4dragunov/leaksensor/src/apps/LeakDetector/SRWLD02/sensors.h

/*
 * sensors.h
 *
 *  Created on: Feb 3, 2025
 *      Author: Andrey
 */

#ifndef SRC_APPS_SMARTROOF_LORA_NODE_LEAKDETECTOR_SRWLD01_SENSORS_H_
#define SRC_APPS_SMARTROOF_LORA_NODE_LEAKDETECTOR_SRWLD01_SENSORS_H_
#include <chrono>
#include "sensors-board.h"
#define MAX_DS18B20_SENSOR_COUNT 8
typedef struct {
	int16_t data[MAX_DS18B20_SENSOR_COUNT];
	uint8_t sensors;
	std::chrono::time_point<std::chrono::system_clock> timestamp;
} ThermalSensorsData ;

typedef struct{
	Samples leakSamples;
	ThermalSensorsData thermal;
	std::chrono::time_point<std::chrono::system_clock> timestamp;
}SummarySensorsData;

extern osMailQId  gSummarySensorsMq;

struct SummarySensorsDataMailDeleter {
    void operator()(SummarySensorsData* p) const {
        //std::cout << std::endl;
        osMailFree(gSummarySensorsMq, p);
    }
};
typedef std::shared_ptr<SummarySensorsData> SummarySensorsDataSharedMail;

#endif /* SRC_APPS_SMARTROOF_LORA_NODE_LEAKDETECTOR_SRWLD01_SENSORS_H_ */
