4dragunov/leaksensor/src/boards/SRWLD01/board-config.h

/*!
 * \file      board-config.h
 *
 * \brief     Board configuration
 *
 * \copyright Revised BSD License, see section \ref LICENSE.
 *
 * \code
 *                ______                              _
 *               / _____)             _              | |
 *              ( (____  _____ ____ _| |_ _____  ____| |__
 *               \____ \| ___ |    (_   _) ___ |/ ___)  _ \
 *               _____) ) ____| | | || |_| ____( (___| | | |
 *              (______/|_____)_|_|_| \__)_____)\____)_| |_|
 *              (C)2013-2017 Semtech
 *
 *               ___ _____ _   ___ _  _____ ___  ___  ___ ___
 *              / __|_   _/_\ / __| |/ / __/ _ \| _ \/ __| __|
 *              \__ \ | |/ _ \ (__| ' <| _| (_) |   / (__| _|
 *              |___/ |_/_/ \_\___|_|\_\_| \___/|_|_\\___|___|
 *              embedded.connectivity.solutions===============
 *
 * \endcode
 *
 * \author    Miguel Luis ( Semtech )
 *
 * \author    Gregory Cristian ( Semtech )
 *
 * \author    Daniel Jaeckle ( STACKFORCE )
 *
 * \author    Johannes Bruder ( STACKFORCE )
 */
#ifndef __BOARD_CONFIG_H__
#define __BOARD_CONFIG_H__

#include "gpio.h"
#include "adc.h"
#include "OneWire.h"
#include "ds18b20.h"
#include "modbus.h"
#include "eeprom.h"
#include "sensors-board.h"
/*!
 * Defines the time required for the TCXO to wakeup [ms].
 */
#if defined( SX1262MBXDAS )
#define BOARD_TCXO_WAKEUP_TIME                      5
#else
#define BOARD_TCXO_WAKEUP_TIME                      0
#endif

/*!
 * Board MCU pins definitions
 */
#define RADIO_RESET                                 PB_12

#define RADIO_MOSI                                  PB_15
#define RADIO_MISO                                  PB_14
#define RADIO_SCLK                                  PB_13

#if defined( SX1272MB2DAS) || defined( SX1276MB1LAS ) || defined( SX1276MB1MAS )

#define RADIO_NSS                                   PD_8

#define RADIO_DIO_0                                 PE_6
#define RADIO_DIO_1                                 PE_3
#define RADIO_DIO_2                                 PE_4

//#define RADIO_DIO_3
//#define RADIO_DIO_4
//#define RADIO_DIO_5

//#define RADIO_ANT_SWITCH

// Debug pins definition.
#define RADIO_DBG_PIN_TX
#define RADIO_DBG_PIN_RX

#endif

#define LED_1                                       PF_11
#define LED_2                                       PF_12
#define LED_3                                       PG_0

typedef enum {
	LED1 = 0,
	LED2,
	LED3
} LedsType;

#define LED_ON  1
#define LED_OFF 0
#define OSC_LSE_IN                                  PC_14
#define OSC_LSE_OUT                                 PC_15

//#define OSC_HSE_IN                                  PH_0
//#define OSC_HSE_OUT                                 PH_1

#define SWCLK                                       PA_14
#define SWDAT                                       PA_13

//#define I2C_SCL                                     PB_8
//#define I2C_SDA                                     PB_9
//usart2
#define RS485_TX                                     PD_5
#define RS485_RX                                     PD_6
//usart1
#define OW_RX                                    PB_7
#define OW_TX                                    PB_6

//Power delivery pin to control external power switch
//Used only if defined and set
//#define OW_PD
//#define OW_PD_ON                                1

#define BAT_PWR                                  PF_3

#define SYS_CHANNEL_COUNT  2
#define WL_CHANNEL_COUNT  20
#define ADC_CHANNEL_COUNT  (WL_CHANNEL_COUNT + SYS_CHANNEL_COUNT)

#endif // __BOARD_CONFIG_H__
