4dragunov/leaksensor/src/boards/mcu/stm32/STM32WLxx_HAL_Driver/Inc/stm32wlxx_hal.h

/**
  ******************************************************************************
  * @file    stm32wlxx_hal.h
  * @author  MCD Application Team
  * @brief   This file contains all the functions prototypes for the HAL
  *          module driver.
  ******************************************************************************
  * @attention
  *
  * <h2><center>&copy; Copyright (c) 2020 STMicroelectronics.
  * All rights reserved.</center></h2>
  *
  * This software component is licensed by ST under BSD 3-Clause license,
  * the "License"; You may not use this file except in compliance with the
  * License. You may obtain a copy of the License at:
  *                       opensource.org/licenses/BSD-3-Clause
  *
  ******************************************************************************
  */

/* Define to prevent recursive inclusion -------------------------------------*/
#ifndef __STM32WLxx_HAL_H
#define __STM32WLxx_HAL_H

#ifdef __cplusplus
extern "C" {
#endif

/* Includes ------------------------------------------------------------------*/
#include "stm32wlxx_hal_conf.h"
#include "stm32wlxx_ll_system.h"

/** @addtogroup STM32WLxx_HAL_Driver
  * @{
  */

/** @defgroup HAL HAL
  * @{
  */

/* Exported types ------------------------------------------------------------*/
/** @defgroup HAL_Exported_Structures HAL Exported Structures
  * @{
  */

/** @defgroup HAL_TICK_FREQ Tick Frequency
  * @{
  */
typedef enum
{
  HAL_TICK_FREQ_10HZ         = 100U,
  HAL_TICK_FREQ_100HZ        = 10U,
  HAL_TICK_FREQ_1KHZ         = 1U,
  HAL_TICK_FREQ_DEFAULT      = HAL_TICK_FREQ_1KHZ
} HAL_TickFreqTypeDef;
/**
  * @}
  */

#if defined(DUAL_CORE)
/** @defgroup HAL_SYSCFG_IM HAL SYSCFG Interrupt Mask
  * @{
  */
/**
  * @brief SYSCFG Interrupt Mask structure definition
  */
typedef struct
{
  uint32_t InterruptMask1;      /*!< The SYSCFG Interrupt Mask to be configured.
                                     This parameter can be a combination of @ref SYSCFG_IM_GRP1 */
  uint32_t InterruptMask2;      /*!< The SYSCFG Interrupt Mask to be configured.
                                     This parameter can be a combination of @ref SYSCFG_IM_GRP2 */
} SYSCFG_InterruptTypeDef;
/**
  * @}
  */
#endif

/**
  * @}
  */


/* Exported constants --------------------------------------------------------*/
/** @defgroup HAL_Exported_Constants HAL Exported Constants
  * @{
  */

/** @defgroup SYSCFG_Exported_Constants SYSCFG Exported Constants
  * @{
  */

/** @defgroup SYSCFG_BootMode BOOT Mode
  * @{
  */
#define SYSCFG_BOOT_MAINFLASH           LL_SYSCFG_REMAP_FLASH           /*!< Main Flash memory mapped at 0x00000000   */
#define SYSCFG_BOOT_SYSTEMFLASH         LL_SYSCFG_REMAP_SYSTEMFLASH     /*!< System Flash memory mapped at 0x00000000 */
#define SYSCFG_BOOT_SRAM                LL_SYSCFG_REMAP_SRAM            /*!< SRAM1 mapped at 0x00000000               */
/**
  * @}
  */

/** @defgroup SYSCFG_SRAM2WRP SRAM2 Page Write protection (0 to 31)
  * @{
  */
#define SYSCFG_SRAM2WRP_PAGE0           LL_SYSCFG_SRAM2WRP_PAGE0        /*!< SRAM2 Write protection page 0  */
#define SYSCFG_SRAM2WRP_PAGE1           LL_SYSCFG_SRAM2WRP_PAGE1        /*!< SRAM2 Write protection page 1  */
#define SYSCFG_SRAM2WRP_PAGE2           LL_SYSCFG_SRAM2WRP_PAGE2        /*!< SRAM2 Write protection page 2  */
#define SYSCFG_SRAM2WRP_PAGE3           LL_SYSCFG_SRAM2WRP_PAGE3        /*!< SRAM2 Write protection page 3  */
#define SYSCFG_SRAM2WRP_PAGE4           LL_SYSCFG_SRAM2WRP_PAGE4        /*!< SRAM2 Write protection page 4  */
#define SYSCFG_SRAM2WRP_PAGE5           LL_SYSCFG_SRAM2WRP_PAGE5        /*!< SRAM2 Write protection page 5  */
#define SYSCFG_SRAM2WRP_PAGE6           LL_SYSCFG_SRAM2WRP_PAGE6        /*!< SRAM2 Write protection page 6  */
#define SYSCFG_SRAM2WRP_PAGE7           LL_SYSCFG_SRAM2WRP_PAGE7        /*!< SRAM2 Write protection page 7  */
#define SYSCFG_SRAM2WRP_PAGE8           LL_SYSCFG_SRAM2WRP_PAGE8        /*!< SRAM2 Write protection page 8  */
#define SYSCFG_SRAM2WRP_PAGE9           LL_SYSCFG_SRAM2WRP_PAGE9        /*!< SRAM2 Write protection page 9  */
#define SYSCFG_SRAM2WRP_PAGE10          LL_SYSCFG_SRAM2WRP_PAGE10       /*!< SRAM2 Write protection page 10 */
#define SYSCFG_SRAM2WRP_PAGE11          LL_SYSCFG_SRAM2WRP_PAGE11       /*!< SRAM2 Write protection page 11 */
#define SYSCFG_SRAM2WRP_PAGE12          LL_SYSCFG_SRAM2WRP_PAGE12       /*!< SRAM2 Write protection page 12 */
#define SYSCFG_SRAM2WRP_PAGE13          LL_SYSCFG_SRAM2WRP_PAGE13       /*!< SRAM2 Write protection page 13 */
#define SYSCFG_SRAM2WRP_PAGE14          LL_SYSCFG_SRAM2WRP_PAGE14       /*!< SRAM2 Write protection page 14 */
#define SYSCFG_SRAM2WRP_PAGE15          LL_SYSCFG_SRAM2WRP_PAGE15       /*!< SRAM2 Write protection page 15 */
#define SYSCFG_SRAM2WRP_PAGE16          LL_SYSCFG_SRAM2WRP_PAGE16       /*!< SRAM2 Write protection page 16 */
#define SYSCFG_SRAM2WRP_PAGE17          LL_SYSCFG_SRAM2WRP_PAGE17       /*!< SRAM2 Write protection page 17 */
#define SYSCFG_SRAM2WRP_PAGE18          LL_SYSCFG_SRAM2WRP_PAGE18       /*!< SRAM2 Write protection page 18 */
#define SYSCFG_SRAM2WRP_PAGE19          LL_SYSCFG_SRAM2WRP_PAGE19       /*!< SRAM2 Write protection page 19 */
#define SYSCFG_SRAM2WRP_PAGE20          LL_SYSCFG_SRAM2WRP_PAGE20       /*!< SRAM2 Write protection page 20 */
#define SYSCFG_SRAM2WRP_PAGE21          LL_SYSCFG_SRAM2WRP_PAGE21       /*!< SRAM2 Write protection page 21 */
#define SYSCFG_SRAM2WRP_PAGE22          LL_SYSCFG_SRAM2WRP_PAGE22       /*!< SRAM2 Write protection page 22 */
#define SYSCFG_SRAM2WRP_PAGE23          LL_SYSCFG_SRAM2WRP_PAGE23       /*!< SRAM2 Write protection page 23 */
#define SYSCFG_SRAM2WRP_PAGE24          LL_SYSCFG_SRAM2WRP_PAGE24       /*!< SRAM2 Write protection page 24 */
#define SYSCFG_SRAM2WRP_PAGE25          LL_SYSCFG_SRAM2WRP_PAGE25       /*!< SRAM2 Write protection page 25 */
#define SYSCFG_SRAM2WRP_PAGE26          LL_SYSCFG_SRAM2WRP_PAGE26       /*!< SRAM2 Write protection page 26 */
#define SYSCFG_SRAM2WRP_PAGE27          LL_SYSCFG_SRAM2WRP_PAGE27       /*!< SRAM2 Write protection page 27 */
#define SYSCFG_SRAM2WRP_PAGE28          LL_SYSCFG_SRAM2WRP_PAGE28       /*!< SRAM2 Write protection page 28 */
#define SYSCFG_SRAM2WRP_PAGE29          LL_SYSCFG_SRAM2WRP_PAGE29       /*!< SRAM2 Write protection page 29 */
#define SYSCFG_SRAM2WRP_PAGE30          LL_SYSCFG_SRAM2WRP_PAGE30       /*!< SRAM2 Write protection page 30 */
#define SYSCFG_SRAM2WRP_PAGE31          LL_SYSCFG_SRAM2WRP_PAGE31       /*!< SRAM2 Write protection page 31 */

/**
  * @}
  */

#if defined(VREFBUF)
/** @defgroup SYSCFG_VREFBUF_VoltageScale VREFBUF Voltage Scale
  * @{
  */
#define SYSCFG_VREFBUF_VOLTAGE_SCALE0   LL_VREFBUF_VOLTAGE_SCALE0       /*!< Voltage reference scale 0 (VREF_OUT1) */
#define SYSCFG_VREFBUF_VOLTAGE_SCALE1   LL_VREFBUF_VOLTAGE_SCALE1       /*!< Voltage reference scale 1 (VREF_OUT2) */

/**
  * @}
  */

/** @defgroup SYSCFG_VREFBUF_HighImpedance VREFBUF High Impedance
  * @{
  */
#define SYSCFG_VREFBUF_HIGH_IMPEDANCE_DISABLE   0x00000000U             /*!< VREF_plus pin is internally connected to Voltage reference buffer output */
#define SYSCFG_VREFBUF_HIGH_IMPEDANCE_ENABLE    VREFBUF_CSR_HIZ         /*!< VREF_plus pin is high impedance */

/**
  * @}
  */
#endif /* VREFBUF */

/** @defgroup SYSCFG_SRAM_flags_definition SRAM Flags
  * @{
  */

#define SYSCFG_FLAG_SRAM2_PE            SYSCFG_CFGR2_SPF                /*!< SRAM2 parity error */
#define SYSCFG_FLAG_SRAM_BUSY           SYSCFG_SCSR_SRAMBSY             /*!< SRAM1 or SRAM2 erase operation is ongoing */
#define SYSCFG_FLAG_PKASRAM_BUSY        SYSCFG_SCSR_PKASRAMBSY          /*!< PKA SRAM busy by erase operation */
/**
  * @}
  */

/** @defgroup SYSCFG_FastModePlus_GPIO Fast-mode Plus on GPIO
  * @{
  */

/** @brief  Fast-mode Plus driving capability on a specific GPIO
  */
#define SYSCFG_FASTMODEPLUS_PB6         SYSCFG_CFGR1_I2C_PB6_FMP        /*!< Enable Fast-mode Plus on PB6 */
#define SYSCFG_FASTMODEPLUS_PB7         SYSCFG_CFGR1_I2C_PB7_FMP        /*!< Enable Fast-mode Plus on PB7 */
#define SYSCFG_FASTMODEPLUS_PB8         SYSCFG_CFGR1_I2C_PB8_FMP        /*!< Enable Fast-mode Plus on PB8 */
#define SYSCFG_FASTMODEPLUS_PB9         SYSCFG_CFGR1_I2C_PB9_FMP        /*!< Enable Fast-mode Plus on PB9 */

/**
 * @}
 */

#if defined(DUAL_CORE)
/** @defgroup SYSCFG_IM_GRP1 SYSCFG INTERRUPT MASK GROUP1
  * @{
  */

#define HAL_SYSCFG_GRP1_RESERVED                0x00U                              /*!< Define user to differentiate Group1 to Group 2                */

#if defined(CORE_CM0PLUS)
/** @brief  Interrupt mask related to CPU2 NVIC
  */
#define HAL_SYSCFG_GRP1_RTCSTAMP_RTCTAMP_LSECSS  (LL_C2_SYSCFG_GRP1_RTCSTAMP_RTCTAMP_LSECSS | HAL_SYSCFG_GRP1_RESERVED)  /*!< Enabling of interrupt from RTC TimeStamp, RTC Tampers
                                                                                                                              and LSE Clock Security System to CPU2               */
#define HAL_SYSCFG_GRP1_RTCALARM                (LL_C2_SYSCFG_GRP1_RTCALARM        | HAL_SYSCFG_GRP1_RESERVED) /*!< Enabling of interrupt from RTC Alarms to CPU2                 */
#define HAL_SYSCFG_GRP1_RTCSSRU                 (LL_C2_SYSCFG_GRP1_RTCSSRU         | HAL_SYSCFG_GRP1_RESERVED) /*!< Enabling of interrupt from RTC SSRU to CPU2                   */
#define HAL_SYSCFG_GRP1_RTCWKUP                 (LL_C2_SYSCFG_GRP1_RTCWKUP         | HAL_SYSCFG_GRP1_RESERVED) /*!< Enabling of interrupt from RTC Wakeup to CPU2                 */
#define HAL_SYSCFG_GRP1_RCC                     (LL_C2_SYSCFG_GRP1_RCC             | HAL_SYSCFG_GRP1_RESERVED) /*!< Enabling of interrupt from RCC to CPU2                        */
#define HAL_SYSCFG_GRP1_FLASH                   (LL_C2_SYSCFG_GRP1_FLASH           | HAL_SYSCFG_GRP1_RESERVED) /*!< Enabling of interrupt from FLASH to CPU2                      */
#define HAL_SYSCFG_GRP1_PKA                     (LL_C2_SYSCFG_GRP1_PKA             | HAL_SYSCFG_GRP1_RESERVED) /*!< Enabling of interrupt from PKA to CPU2                        */
#define HAL_SYSCFG_GRP1_AES                     (LL_C2_SYSCFG_GRP1_AES             | HAL_SYSCFG_GRP1_RESERVED) /*!< Enabling of interrupt from AES to CPU2                        */
#define HAL_SYSCFG_GRP1_COMP                    (LL_C2_SYSCFG_GRP1_COMP            | HAL_SYSCFG_GRP1_RESERVED) /*!< Enabling of interrupt from Comparator to CPU2                 */
#define HAL_SYSCFG_GRP1_ADC                     (LL_C2_SYSCFG_GRP1_ADC             | HAL_SYSCFG_GRP1_RESERVED) /*!< Enabling of interrupt from Analog Digital Converter to CPU2   */
#define HAL_SYSCFG_GRP1_DAC                     (LL_C2_SYSCFG_GRP1_DAC             | HAL_SYSCFG_GRP1_RESERVED) /*!< Enabling of interrupt from Digital Analog Converter to CPU2   */
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
