4dragunov/leaksensor/src/boards/mcu/stm32/STM32WLxx_HAL_Driver/Inc/stm32wlxx_hal_adc.h

/**
  ******************************************************************************
  * @file    stm32wlxx_hal_adc.h
  * @author  MCD Application Team
  * @brief   Header file of ADC HAL module.
  ******************************************************************************
  * @attention
  *
  * <h2><center>&copy; Copyright (c) 2020 STMicroelectronics.
  * All rights reserved.</center></h2>
  *
  * This software component is licensed by ST under BSD 3-Clause license,
  * the "License"; You may not use this file except in compliance with the
  * License. You may obtain a copy of the License at:
  *                        opensource.org/licenses/BSD-3-Clause
  *
  ******************************************************************************
  */

/* Define to prevent recursive inclusion -------------------------------------*/
#ifndef STM32WLxx_HAL_ADC_H
#define STM32WLxx_HAL_ADC_H

#ifdef __cplusplus
extern "C" {
#endif

/* Includes ------------------------------------------------------------------*/
#include "stm32wlxx_hal_def.h"

/* Include low level driver */
#include "stm32wlxx_ll_adc.h"

/** @addtogroup STM32WLxx_HAL_Driver
  * @{
  */

/** @addtogroup ADC
  * @{
  */

/* Exported types ------------------------------------------------------------*/
/** @defgroup ADC_Exported_Types ADC Exported Types
  * @{
  */

/**
  * @brief  ADC group regular oversampling structure definition
  */
typedef struct
{
  uint32_t Ratio;                         /*!< Configures the oversampling ratio.
                                               This parameter can be a value of @ref ADC_HAL_EC_OVS_RATIO */

  uint32_t RightBitShift;                 /*!< Configures the division coefficient for the Oversampler.
                                               This parameter can be a value of @ref ADC_HAL_EC_OVS_SHIFT */

  uint32_t TriggeredMode;                 /*!< Selects the regular triggered oversampling mode.
                                               This parameter can be a value of @ref ADC_HAL_EC_OVS_DISCONT_MODE */

} ADC_OversamplingTypeDef;
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
